coreyt429/cube_bot_2026/motion_test.py

import logging
from time import sleep

from cube_bot import CubeBot
from maestro import Servo
from arm import Arm

logging.basicConfig(level=logging.DEBUG)
logger = logging.getLogger(__name__)
logger.setLevel(logging.DEBUG)

def up(bot, clockwise=True):
    """Move up surface clockwise"""
    bot.arms['r'].open()
    bot.arms['l'].rotate(180)
    bot.arms['r'].close()
    if clockwise:
        bot.arms['r'].rotate(90)
    else:
        bot.arms['r'].rotate(-90)
    bot.arms['r'].open()
    bot.arms['l'].rotate(-180)


if __name__ == "__main__":
    bot = CubeBot("calibration")
    for arm in bot.arms.values():
        arm.reset()
        arm.open()
    sleep(2)
    for arm in bot.arms.values():
        arm.close()
    up(bot)
    sleep(10)
    up(bot, clockwise=False)   
